KarolWys93/weather-station-wifi/res/error_black.bmp

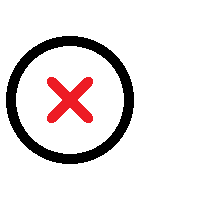
res/error_black.bmp
