KarolWys93/weather-station-wifi/res/fcast_bckgrond.bmp

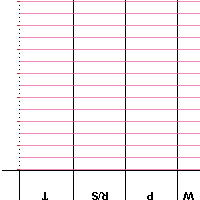
res/fcast_bckgrond.bmp
