KarolWys93/weather-station-wifi/res/low_bat.bmp

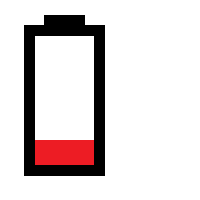
res/low_bat.bmp
