KarolWys93/weather-station-wifi/res/screen.bmp

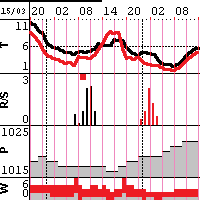
res/screen.bmp
