KarolWys93/weather-station-wifi/res/sd_err.bmp

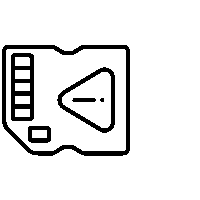
res/sd_err.bmp
