KarolWys93/weather-station-wifi/res/wifi_err.bmp

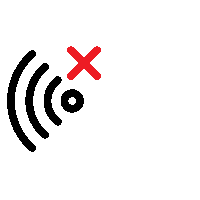
res/wifi_err.bmp
