KarolWys93/weather-station-wifi/Core/Src/rtc.c

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
/* Includes ------------------------------------------------------------------*/
#include "rtc.h"

/* USER CODE BEGIN 0 */

#include "logger.h"
#include "fatfs.h"
#include "system_info.h"
#include "backup_registers.h"
#include "dma.h"

#define RTC_CALIBRATION_HISTORY_SIZE (4)

typedef struct
{
	uint32_t calibratedFreq;
	uint16_t dataReady;
	uint16_t index;
	uint32_t deltaArray[RTC_CALIBRATION_HISTORY_SIZE];
} RTC_Calibration;

/* USER CODE END 0 */

RTC_HandleTypeDef hrtc;

/* RTC init function */
void MX_RTC_Init(void)
{

  RTC_TimeTypeDef sTime = {0};
  RTC_DateTypeDef DateToUpdate = {0};

  /** Initialize RTC Only
  */
  hrtc.Instance = RTC;
  hrtc.Init.AsynchPrediv = RTC_AUTO_1_SECOND;
  hrtc.Init.OutPut = RTC_OUTPUTSOURCE_NONE;
  if (HAL_RTC_Init(&hrtc) != HAL_OK)
  {
    Error_Handler();
  }

  /* USER CODE BEGIN Check_RTC_BKUP */
  return;
  /* USER CODE END Check_RTC_BKUP */

  /** Initialize RTC and set the Time and Date
  */
  sTime.Hours = 0;
  sTime.Minutes = 0;
  sTime.Seconds = 0;

  if (HAL_RTC_SetTime(&hrtc, &sTime, RTC_FORMAT_BIN) != HAL_OK)
  {
    Error_Handler();
  }
  DateToUpdate.WeekDay = RTC_WEEKDAY_MONDAY;
  DateToUpdate.Month = RTC_MONTH_JANUARY;
  DateToUpdate.Date = 1;
  DateToUpdate.Year = 0;

  if (HAL_RTC_SetDate(&hrtc, &DateToUpdate, RTC_FORMAT_BIN) != HAL_OK)
  {
    Error_Handler();
  }
}

void HAL_RTC_MspInit(RTC_HandleTypeDef* rtcHandle)
{

  if(rtcHandle->Instance==RTC)
  {
    HAL_PWR_EnableBkUpAccess();
    /* Enable BKP CLK enable for backup registers */
    __HAL_RCC_BKP_CLK_ENABLE();
    /* RTC clock enable */
    __HAL_RCC_RTC_ENABLE();
  }
}

void HAL_RTC_MspDeInit(RTC_HandleTypeDef* rtcHandle)
{

  if(rtcHandle->Instance==RTC)
  {
    /* Peripheral clock disable */
    __HAL_RCC_RTC_DISABLE();
  }
}

/* USER CODE BEGIN 1 */

//static function prototypes
static void defaultCalibrationData(RTC_Calibration *rtcCalibrationData);
static void loadCalibrationData(RTC_Calibration *rtcCalibrationData);
static void saveCalibrationData(RTC_Calibration *rtcCalibrationData);
static HAL_StatusTypeDef RTC_EnterInitMode(RTC_HandleTypeDef *hrtc);
static HAL_StatusTypeDef RTC_ExitInitMode(RTC_HandleTypeDef *hrtc);



static HAL_StatusTypeDef RTC_EnterInitMode(RTC_HandleTypeDef *hrtc)
{
  uint32_t tickstart = 0U;

  tickstart = HAL_GetTick();
  /* Wait till RTC is in INIT state and if Time out is reached exit */
  while ((hrtc->Instance->CRL & RTC_CRL_RTOFF) == (uint32_t)RESET)
  {
    if ((HAL_GetTick() - tickstart) >  RTC_TIMEOUT_VALUE)
    {
      return HAL_TIMEOUT;
    }
  }

  /* Disable the write protection for RTC registers */
  __HAL_RTC_WRITEPROTECTION_DISABLE(hrtc);


  return HAL_OK;
}

static HAL_StatusTypeDef RTC_ExitInitMode(RTC_HandleTypeDef *hrtc)
{
  uint32_t tickstart = 0U;

  /* Disable the write protection for RTC registers */
  __HAL_RTC_WRITEPROTECTION_ENABLE(hrtc);

  tickstart = HAL_GetTick();
  /* Wait till RTC is in INIT state and if Time out is reached exit */
  while ((hrtc->Instance->CRL & RTC_CRL_RTOFF) == (uint32_t)RESET)
  {
    if ((HAL_GetTick() - tickstart) >  RTC_TIMEOUT_VALUE)
    {
      return HAL_TIMEOUT;
    }
  }

  return HAL_OK;
}


HAL_StatusTypeDef RTC_setTime(time_t time)
{
	  HAL_StatusTypeDef status = HAL_OK;

	  /* Set Initialization mode */
	  if (RTC_EnterInitMode(&hrtc) != HAL_OK)
	  {
	    status = HAL_ERROR;
	  }
	  else
	  {
	    /* Set RTC COUNTER MSB word */
	    WRITE_REG(hrtc.Instance->CNTH, (time >> 16U));
	    /* Set RTC COUNTER LSB word */
	    WRITE_REG(hrtc.Instance->CNTL, (time & RTC_CNTL_RTC_CNT));

	    /* Wait for synchro */
	    if (RTC_ExitInitMode(&hrtc) != HAL_OK)
	    {
	      status = HAL_ERROR;
	    }
	  }

	  return status;
}

time_t RTC_getTime(void)
{
	  uint16_t high1 = 0U, high2 = 0U, low = 0U;
	  uint32_t timecounter = 0U;

	  high1 = READ_REG(hrtc.Instance->CNTH & RTC_CNTH_RTC_CNT);
	  low   = READ_REG(hrtc.Instance->CNTL & RTC_CNTL_RTC_CNT);
	  high2 = READ_REG(hrtc.Instance->CNTH & RTC_CNTH_RTC_CNT);

	  if (high1 != high2)
	  {
	    /* In this case the counter roll over during reading of CNTL and CNTH registers,
	       read again CNTL register then return the counter value */
	    timecounter = (((uint32_t) high2 << 16U) | READ_REG(hrtc.Instance->CNTL & RTC_CNTL_RTC_CNT));
	  }
	  else
	  {
	    /* No counter roll over during reading of CNTL and CNTH registers, counter
	       value is equal to first value of CNTL and CNTH */
	    timecounter = (((uint32_t) high1 << 16U) | low);
	  }

	  return timecounter;
}

HAL_StatusTypeDef RTC_setAlarmTime(time_t time)
{
	  HAL_StatusTypeDef status = HAL_OK;

	  /* Set Initialization mode */
	  if (RTC_EnterInitMode(&hrtc) != HAL_OK)
	  {
	    status = HAL_ERROR;
	  }
	  else
	  {
	    /* Set RTC COUNTER MSB word */
	    WRITE_REG(hrtc.Instance->ALRH, (time >> 16U));
	    /* Set RTC COUNTER LSB word */
	    WRITE_REG(hrtc.Instance->ALRL, (time & RTC_ALRL_RTC_ALR));

	    /* Wait for synchro */
	    if (RTC_ExitInitMode(&hrtc) != HAL_OK)
	    {
	      status = HAL_ERROR;
	    }
	  }

	  return status;
}

time_t RTC_getAlarmTime(void)
{
	  uint16_t high1 = 0U, low = 0U;

	  high1 = READ_REG(hrtc.Instance->ALRH & RTC_CNTH_RTC_CNT);
	  low   = READ_REG(hrtc.Instance->ALRL & RTC_CNTL_RTC_CNT);

	  return (((uint32_t) high1 << 16U) | low);
}



static void defaultCalibrationData(RTC_Calibration *rtcCalibrationData)
{
    DMA_memset(rtcCalibrationData, 0, sizeof(RTC_Calibration));
	rtcCalibrationData->calibratedFreq = HAL_RCCEx_GetPeriphCLKFreq(RCC_PERIPHCLK_RTC);
}

static void loadCalibrationData(RTC_Calibration *rtcCalibrationData)
{
	FIL calibrationDataFile;
	FRESULT result;
	UINT br = 0;

	if(FR_OK == f_open(&calibrationDataFile, FILE_PATH_RTC_CALIBRATION, FA_READ))
	{
		result = f_read(&calibrationDataFile, rtcCalibrationData, sizeof(RTC_Calibration), &br);
		f_close(&calibrationDataFile);
		if(result == FR_OK && br == sizeof(RTC_Calibration))
		{
				return;	//OK
		}
	}
	defaultCalibrationData(rtcCalibrationData);
}

static void saveCalibrationData(RTC_Calibration *rtcCalibrationData)
{
	FIL calibrationDataFile;
	UINT bw = 0;

	if(FR_OK == f_open(&calibrationDataFile, FILE_PATH_RTC_CALIBRATION, FA_CREATE_ALWAYS | FA_WRITE))
	{
		f_write(&calibrationDataFile, rtcCalibrationData, sizeof(RTC_Calibration), &bw);
		f_close(&calibrationDataFile);
	}
}

void RTC_loadCalibratedClock(void)
{
	RTC_Calibration rtcSyncData;
	uint32_t prescaler;

	loadCalibrationData(&rtcSyncData);
	prescaler = rtcSyncData.calibratedFreq - 1;

	if (RTC_EnterInitMode(&hrtc) == HAL_OK)
	{
	    MODIFY_REG(hrtc.Instance->PRLH, RTC_PRLH_PRL, (prescaler >> 16U));
	    MODIFY_REG(hrtc.Instance->PRLL, RTC_PRLL_PRL, (prescaler & RTC_PRLL_PRL));

	    RTC_ExitInitMode(&hrtc);
	}
	Logger(LOG_INF, "RTC clock: %u Hz", rtcSyncData.calibratedFreq);
}

void RTC_calibration(time_t timeBeforeSync, time_t timeAfterSync)
{
	RTC_Calibration rtcSyncData;
	uint32_t lastSyncTime = 0;
	int32_t deltaTime = 0;
	int32_t meanDelta = 0;
	uint32_t newFrequency = 0;

	lastSyncTime = BCKUP_getLastSyncTime();
	BCKUP_setLastSyncTime(timeAfterSync);

	if(lastSyncTime == 0 || (timeBeforeSync-lastSyncTime) < 30*60)			//no last sync or earlier than 30 minutes
		return;

	deltaTime = timeAfterSync - timeBeforeSync;
	deltaTime = (3600 * deltaTime) / (timeBeforeSync-lastSyncTime);	//normalize delta

	loadCalibrationData(&rtcSyncData);
	rtcSyncData.deltaArray[rtcSyncData.index++] = deltaTime;

	Logger(LOG_DBG, "RTC delta %u: %d", rtcSyncData.index, deltaTime);

	if(rtcSyncData.index >= RTC_CALIBRATION_HISTORY_SIZE)
	{
		rtcSyncData.index = 0;
		rtcSyncData.dataReady = 1;
	}

	if(!rtcSyncData.dataReady)	//not enough samples
	{
		saveCalibrationData(&rtcSyncData);
		return;
	}

	for(uint32_t i = 0; i < RTC_CALIBRATION_HISTORY_SIZE; i++)
	{
		meanDelta += rtcSyncData.deltaArray[i];
	}

	meanDelta /= RTC_CALIBRATION_HISTORY_SIZE;

	Logger(LOG_INF, "RTC delta %d s", meanDelta);
	if(meanDelta > -3 && meanDelta < 3)					//error smaller than 0.1% (3.6s/h), calibration not needed
	{
		saveCalibrationData(&rtcSyncData);
		return;
	}

	rtcSyncData.index = 0;
	rtcSyncData.dataReady = 0;

	newFrequency = (rtcSyncData.calibratedFreq * (3600 - meanDelta))/3600;
	rtcSyncData.calibratedFreq = newFrequency;

	Logger(LOG_INF, "RTC new clock %u Hz", newFrequency);
	saveCalibrationData(&rtcSyncData);

	newFrequency -= 1;
	if (RTC_EnterInitMode(&hrtc) == HAL_OK)
	{
	    MODIFY_REG(hrtc.Instance->PRLH, RTC_PRLH_PRL, (newFrequency >> 16U));
	    MODIFY_REG(hrtc.Instance->PRLL, RTC_PRLL_PRL, (newFrequency & RTC_PRLL_PRL));

	    RTC_ExitInitMode(&hrtc);
	}
}

/* USER CODE END 1 */
