KarolWys93/weather-station-wifi/Core/Inc/images.h

/*
 * images.h
 *
 *  Created on: 01.05.2022
 *      Author: Karol
 */

#ifndef IMAGES_H_
#define IMAGES_H_

#include <stdint.h>

typedef enum ERR_IMAGE
{
	ERR_IMG_GENERAL = 0,
	ERR_IMG_MEMORY_CARD,
	ERR_IMG_WIFI
} ERR_IMAGE;

void load_forecastImg_BlackGrey(uint8_t* black_buff, uint8_t* grey_buff);
void load_forecastImg_Red(uint8_t* red_buff);
void show_emptyForecast_image(void);

void save_img_BlackGrey(uint8_t* black_buff, uint8_t* grey_buff);
void save_img_Red(uint8_t* red_buff);

void show_error_image(ERR_IMAGE errImg, char* errText, char* subText);
void show_configMode_image(void);
void show_low_bat_image(void);

void draw_battery_level_black(uint8_t* black_buff, uint8_t batteryLvl, uint8_t isCharging);
void draw_battery_level_red(uint8_t* red_buff, uint8_t batteryLvl, uint8_t isCharging);

#endif /* IMAGES_H_ */
