KarolWys93/weather-station-wifi/Core/Src/app/server/httpServerApp.h

/*
 * httpServerApp.h
 *
 *  Created on: 24.01.2021
 *      Author: Karol
 */

#ifndef HTTPSERVERAPP_H_
#define HTTPSERVERAPP_H_

#include <stdint.h>

// shut down the server after x minutes of inactivity.
#define HTTP_SERVER_INACTIVITY_TIMEOUT (10*60*1000)	//10 minutes

#define HTTP_SERVER_REQUEST_SIZE      1000
#define HTTP_SERVER_RESPONSE_SIZE     2048
#define HTTP_SERVER_REQUEST_PATH_MAX_SIZE (64)
#define HTTP_SERVER_STATIC_PATH       "/html"

uint8_t runServerApp(uint16_t port, uint8_t maxConnection, uint16_t serverTimeout);

#endif /* HTTPSERVERAPP_H_ */
